YO3BN/digiclock/schematic/schematic.sch

## KiCad design schematic/schematic.sch (2019-09-04)

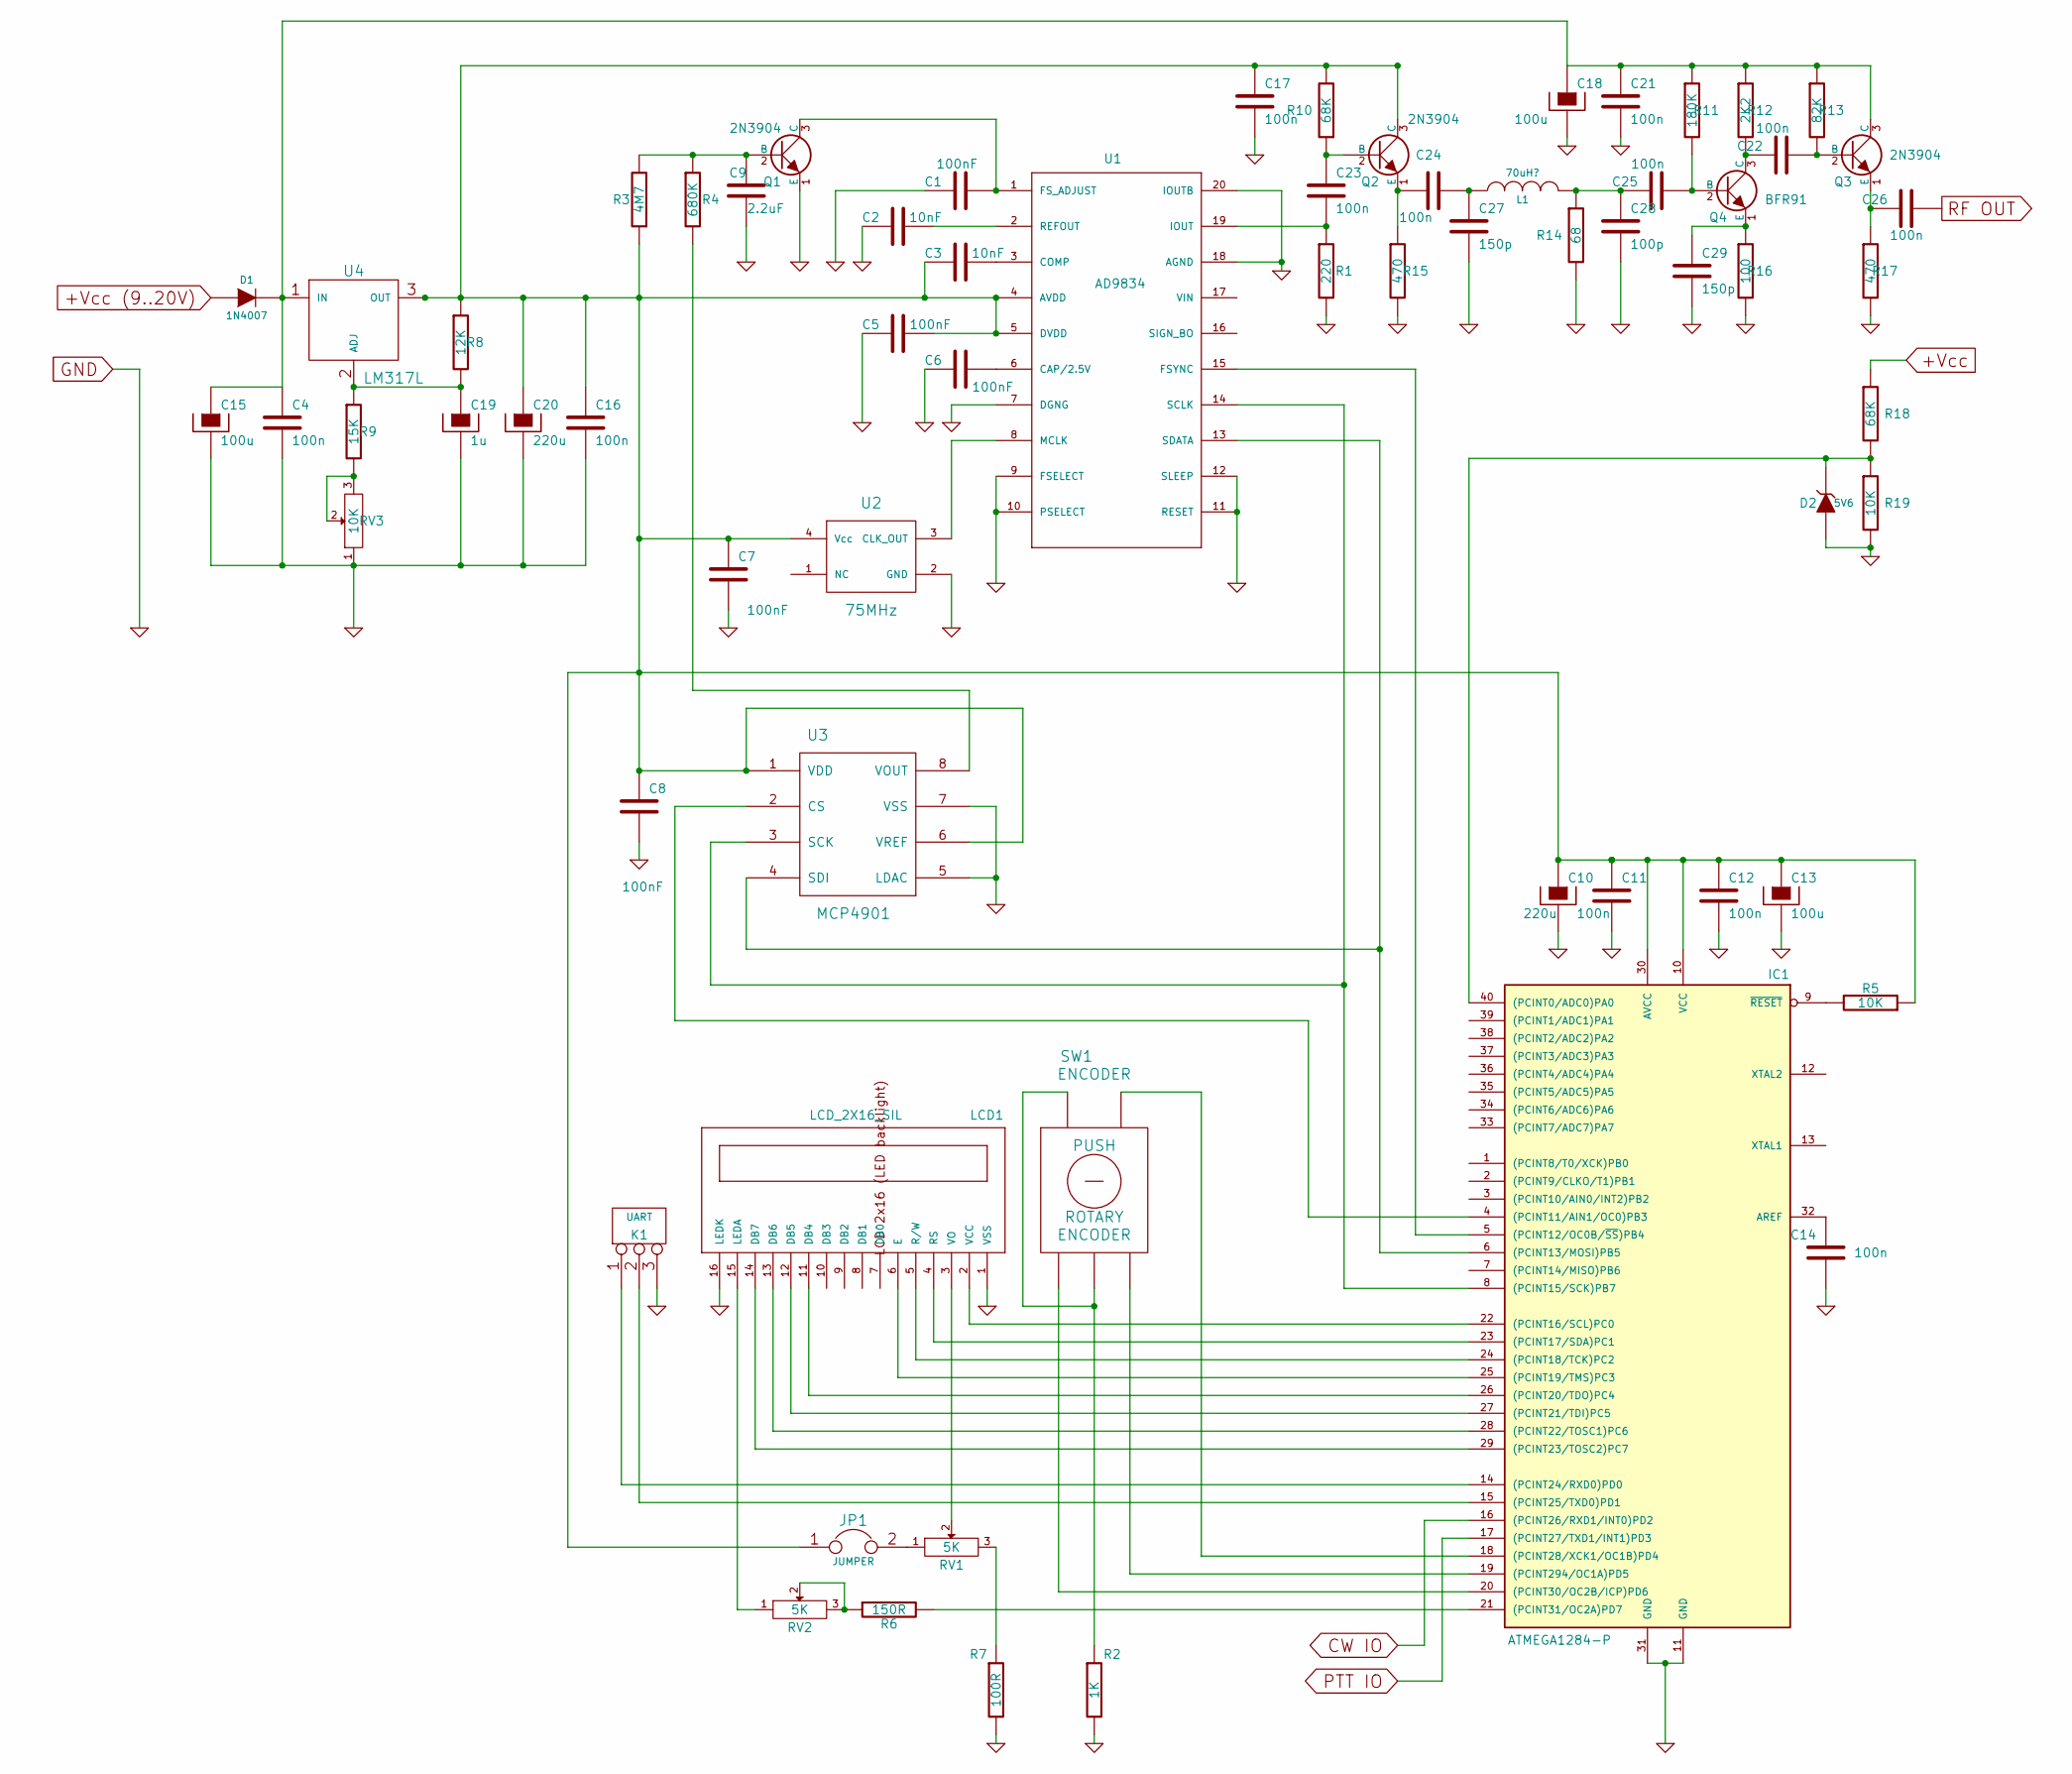
[picture p4: schematic schematic.sch]

Parts:
C1, C5, C6, C7, C8: 100nF
C2, C3: 10nF
C4, C11, C12, C14, C16, C17, C21, C22, C23, C24, C25, C26: 100n
C9: 2.2uF
C10, C20: 220u
C13, C15, C18: 100u
C19: 1u
C27, C29: 150p
C28: 100p
D1: 1N4007
D2: 5V6
IC1: ATMEGA1284-P; DIL40
JP1: JUMPER
K1: UART
L1: 70uH?
LCD1: LCD_2X16_SIL; lcd_2x16_led_backlight-HY-1602F
Q1, Q2, Q3: 2N3904
Q4: BFR91
R1: 220
R2: 1K
R3: 4M7
R4: 680K
R5, R19: 10K
R6: 150R
R7: 100R
R8: 12K
R9: 15K
R10, R18: 68K
R11: 180K
R12: 2K2
R13: 82K
R14: 68
R15, R17: 470
R16: 100
RV1, RV2: 5K
RV3: 10K
SW1: ENCODER
U1: AD9834; ad9834-TSSOP20
U2: 75MHz
U3: MCP4901
U4: LM317L

Connections:
+Vcc: R18.1
+Vcc (9..20V): D1.1 (A)
CW IO: IC1.16 ((PCINT26/RXD1/INT0)PD2)
GND: C1.1, C2.1, C4.2, C5.1, C6.1, C7.2, C8.2, C9.2, C10.2, C11.2, C12.2, C13.2, C14.2, C15.2, C16.2, C17.2, C18.2, C19.2, C20.2, C21.2, C27.2, C28.2, C29.2, D2.1 (A), IC1.11 (GND), IC1.31 (GND), K1.3, LCD1.1 (VSS), LCD1.16 (LEDK), Q1.1 (E), R1.2, R2.2, R7.2, R14.2, R15.2, R16.2, R17.2, R19.2, RV3.1, U1.7 (DGNG), U1.9 (FSELECT), U1.10 (PSELECT), U1.11 (RESET), U1.12 (SLEEP), U1.18 (AGND), U1.20 (IOUTB), U2.2 (GND), U3.5 (LDAC), U3.7 (VSS)
unnamed: C1.2, Q1.3 (C), U1.1 (FS_ADJUST)
unnamed: C2.2, U1.2 (REFOUT)
unnamed: C3.2, U1.3 (COMP)
unnamed: C6.2, U1.6 (CAP/2.5V)
unnamed: C9.1, Q1.2 (B), R3.2, R4.1
unnamed: C3.1, C5.2, C7.1, C8.1, C10.1, C11.1, C12.1, C13.1, C16.1, C17.1, C20.1, IC1.10 (VCC), IC1.30 (AVCC), JP1.1, Q2.3 (C), R3.1, R5.1, R8.1, R10.2, U1.4 (AVDD), U1.5 (DVDD), U2.4 (Vcc), U3.1 (VDD), U3.6 (VREF), U4.3 (OUT)
unnamed: C14.1, IC1.32 (AREF)
unnamed: C4.1, C15.1, C18.1, C21.1, D1.2 (K), Q3.3 (C), R11.1, R12.1, R13.1, U4.1 (IN)
unnamed: C19.1, R8.2, R9.1, U4.2 (ADJ)
unnamed: C22.1, Q4.3 (C), R12.2
unnamed: C22.2, Q3.2 (B), R13.2
unnamed: C23.1, Q2.2 (B), R10.1
unnamed: C23.2, R1.1, U1.19 (IOUT)
unnamed: C24.1, Q2.1 (E), R15.1
unnamed: C24.2, C27.1, L1.1
unnamed: C25.1, C28.1, L1.2, R14.1
unnamed: C25.2, Q4.2 (B), R11.2
unnamed: C26.1, Q3.1 (E), R17.1
unnamed: C29.1, Q4.1 (E), R16.1
unnamed: D2.2 (K), IC1.40 ((PCINT0/ADC0)PA0), R18.2, R19.1
unnamed: IC1.4 ((PCINT11/AIN1/OC0)PB3), U3.2 (CS)
unnamed: IC1.5 ((PCINT12/OC0B/~SS~)PB4), U1.15 (FSYNC)
unnamed: IC1.6 ((PCINT13/MOSI)PB5), U1.13 (SDATA), U3.4 (SDI)
unnamed: IC1.8 ((PCINT15/SCK)PB7), U1.14 (SCLK), U3.3 (SCK)
unnamed: IC1.9 (~RESET), R5.2
unnamed: IC1.14 ((PCINT24/RXD0)PD0), K1.1
unnamed: IC1.15 ((PCINT25/TXD0)PD1), K1.2 (PM)
unnamed: IC1.18 ((PCINT28/XCK1/OC1B)PD4), SW1.~
unnamed: IC1.19 ((PCINT294/OC1A)PD5), SW1.~
unnamed: IC1.20 ((PCINT30/OC2B/ICP)PD6), SW1.~
unnamed: IC1.21 ((PCINT31/OC2A)PD7), R6.2
unnamed: IC1.22 ((PCINT16/SCL)PC0), LCD1.2 (VCC)
unnamed: IC1.23 ((PCINT17/SDA)PC1), LCD1.4 (RS)
unnamed: IC1.24 ((PCINT18/TCK)PC2), LCD1.5 (R/W)
unnamed: IC1.25 ((PCINT19/TMS)PC3), LCD1.6 (E)
unnamed: IC1.26 ((PCINT20/TDO)PC4), LCD1.11 (DB4)
unnamed: IC1.27 ((PCINT21/TDI)PC5), LCD1.12 (DB5)
unnamed: IC1.28 ((PCINT22/TOSC1)PC6), LCD1.13 (DB6)
unnamed: IC1.29 ((PCINT23/TOSC2)PC7), LCD1.14 (DB7)
unnamed: JP1.2, RV1.1
unnamed: LCD1.3 (VO), RV1.2
unnamed: LCD1.15 (LEDA), RV2.1
unnamed: R2.1, SW1.~
unnamed: R4.2, U3.8 (VOUT)
unnamed: R6.1, RV2.2, RV2.3
unnamed: R7.1, RV1.3
unnamed: R9.2, RV3.2, RV3.3
unnamed: U1.8 (MCLK), U2.3 (CLK_OUT)
PTT IO: IC1.17 ((PCINT27/TXD1/INT1)PD3)
RF OUT: C26.2
