YO3BN/digiclock/src/config.h

/*
 * config.h
 *
 *  Created on: Mar 19, 2020
 *      Author: yo3bn
 */

#ifndef SRC_KERNEL_INCLUDE_CONFIG_H_
#define SRC_KERNEL_INCLUDE_CONFIG_H_


/* TODO #errors here for undefined. */
/* TODO #error*/

#define CONFIG_MAX_EVENTS     50

/* TODO */

#define CONFIG_SEM_MAX_TASKS      10

/* TODO */

#define CONFIG_TASK_MAX_NAME  10

/* TODO */

//#define CONFIG_STACK_START_ADDRESS 0x897 // TODO: find this automatically.
#define CONFIG_STACK_DEFAULT_SIZE 512


#endif /* SRC_KERNEL_INCLUDE_CONFIG_H_ */
